L4g0/MiDispositivoMIDI_A3C/04_img/bot.png

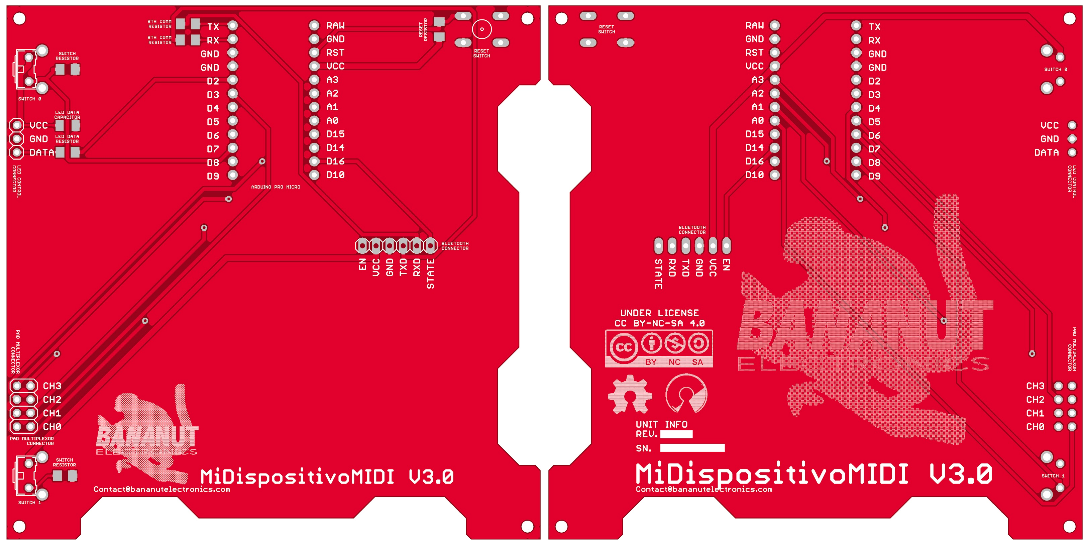
04_img/bot.png
