L4g0/MiDispositivoMIDI_A3C/04_img/front.jpg

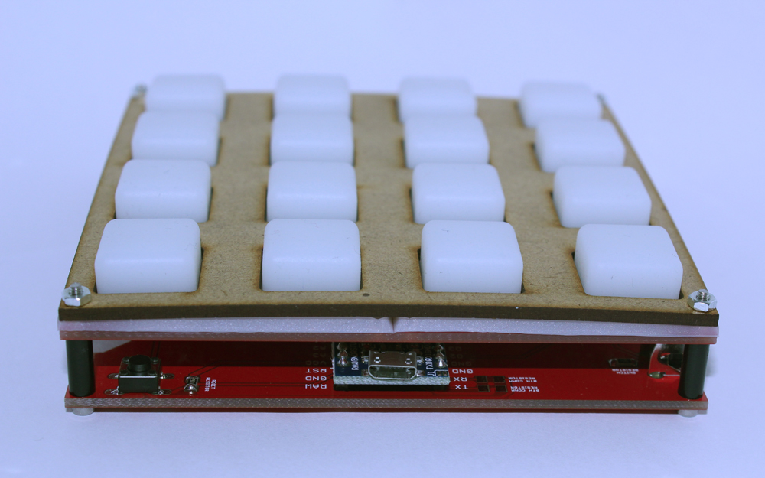
04_img/front.jpg
