L4g0/MiDispositivoMIDI_A3C/04_img/green.jpg

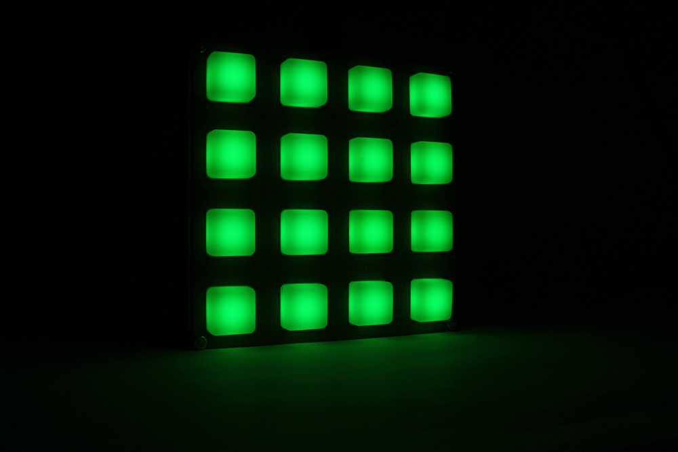
04_img/green.jpg
