L4g0/MiDispositivoMIDI_A3C/04_img/MDM_V3_HW_Render.PNG

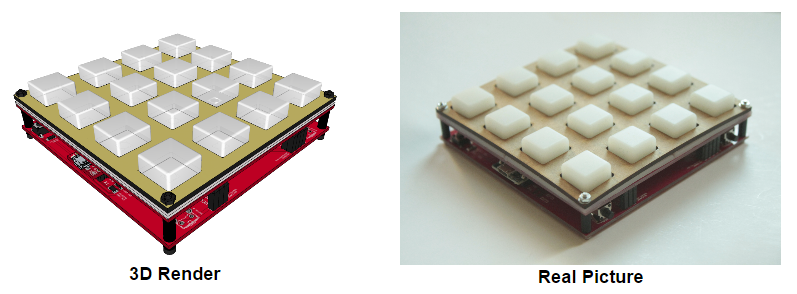
04_img/MDM_V3_HW_Render.PNG
