L4g0/MiDispositivoMIDI_A3C/04_img/MDM_V3_INTRO_Workshop_0.png

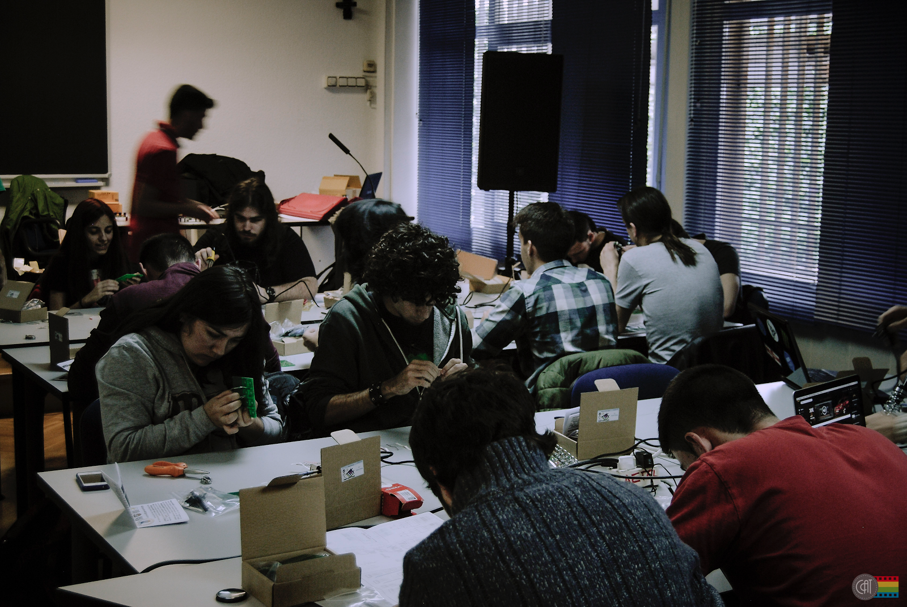
04_img/MDM_V3_INTRO_Workshop_0.png
