L4g0/MiDispositivoMIDI_A3C/04_img/MDM_V3_INTROWorkshop_1.png

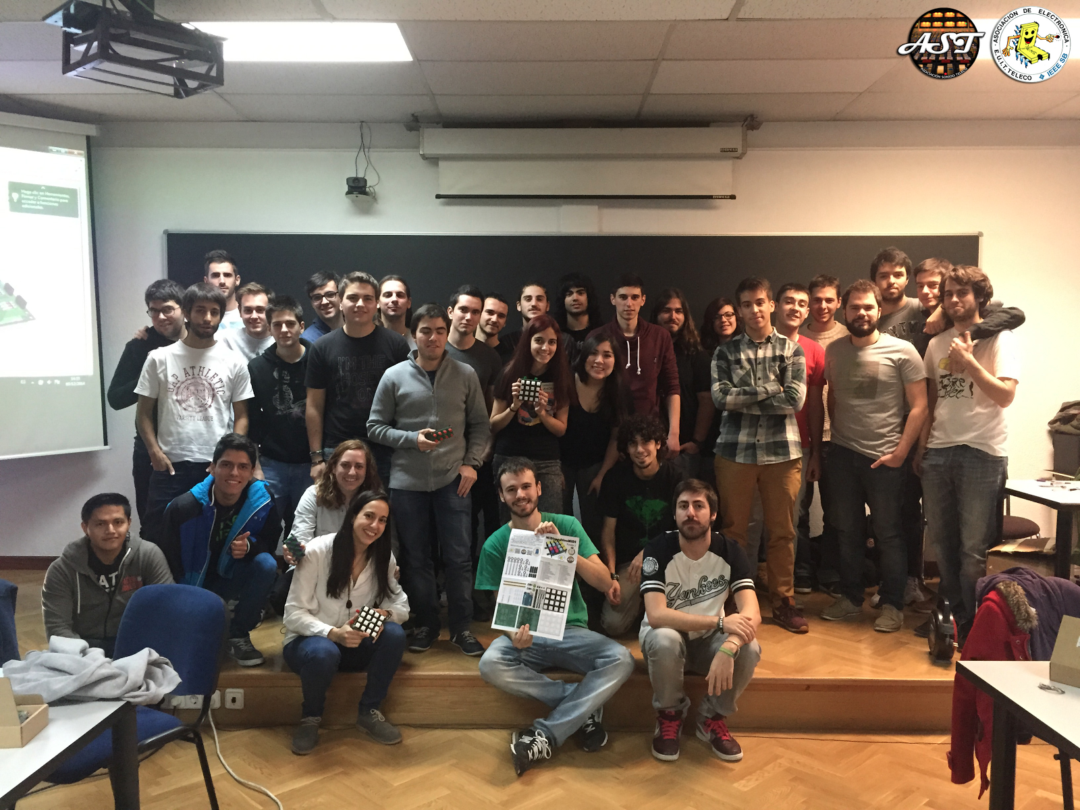
04_img/MDM_V3_INTROWorkshop_1.png
