L4g0/MiDispositivoMIDI_A3C/04_img/touchpads.JPG

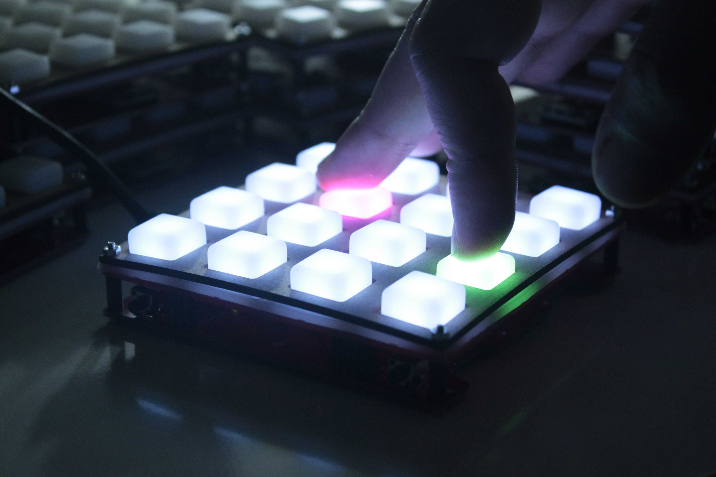
04_img/touchpads.JPG
