L4g0/MiDispositivoMIDI_A3C/04_img/yellow.jpg

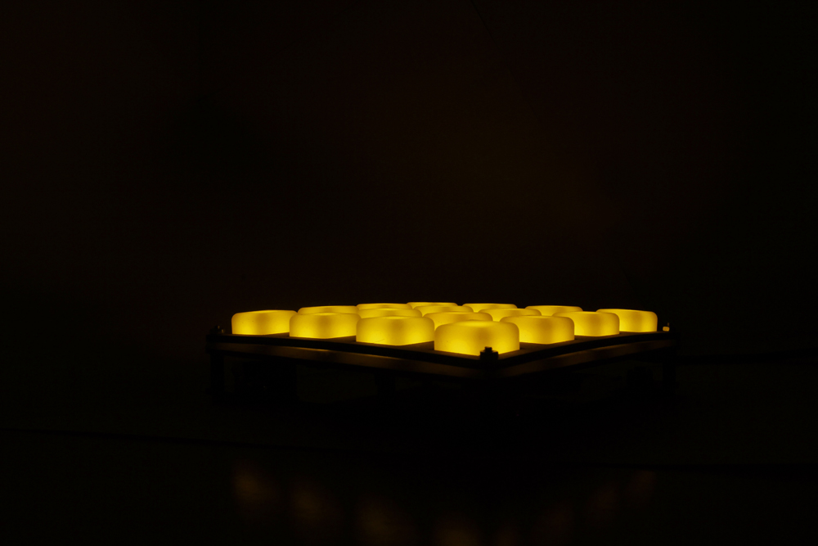
04_img/yellow.jpg
