L4g0/MiDispositivoMIDI_A3C/04_img/components.png

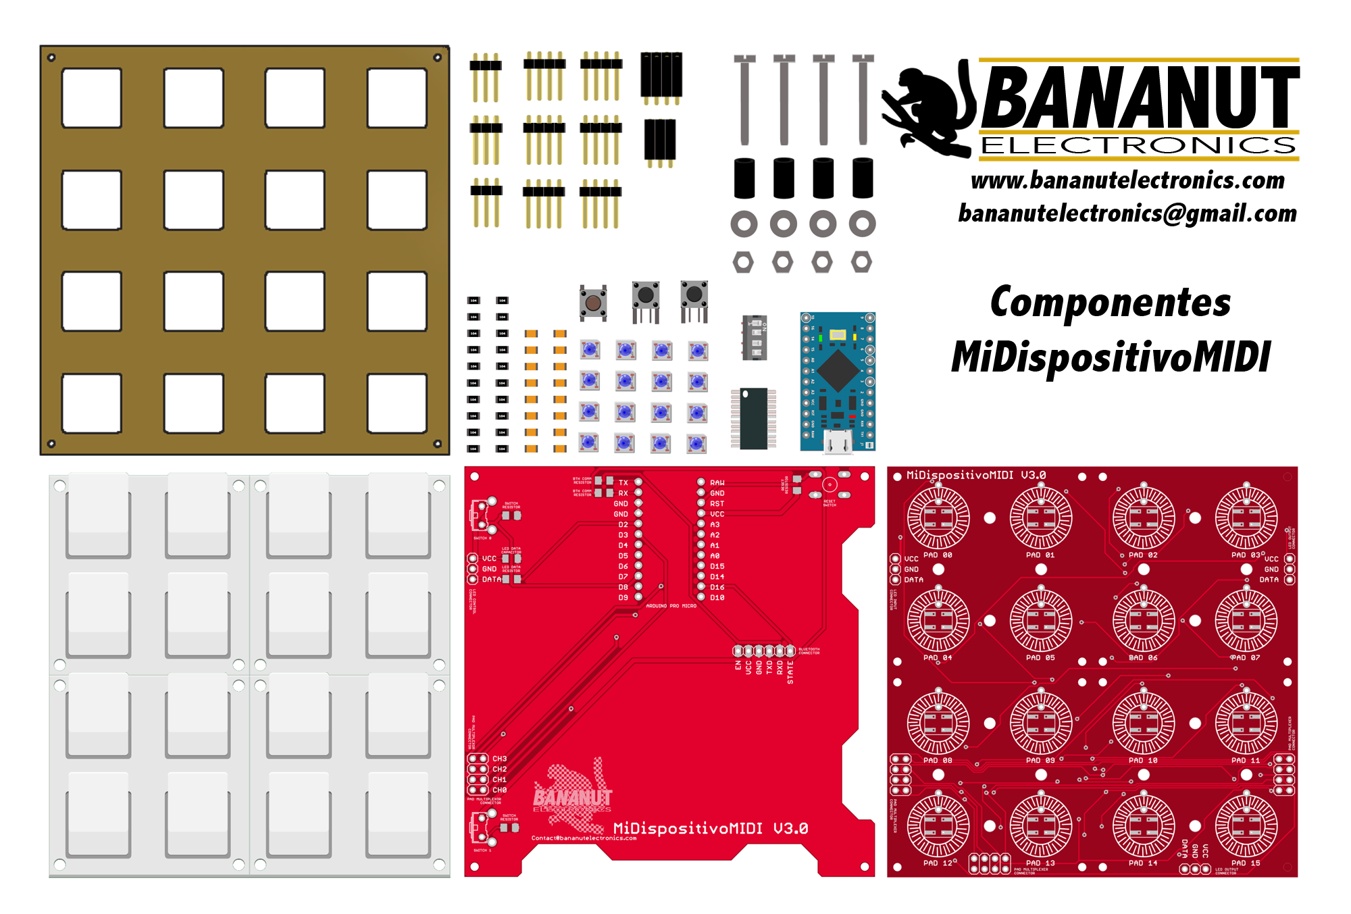
04_img/components.png
