L4g0/MiDispositivoMIDI_A3C/02_hw/01_MDM_V3_LEDPad/tags/A_MDM_V3_LEDPad/MDM_V3_LEDPad_A.sch

## EAGLE design 02_hw/01_MDM_V3_LEDPad/tags/A_MDM_V3_LEDPad/MDM_V3_LEDPad_A.sch (2017-02-17)

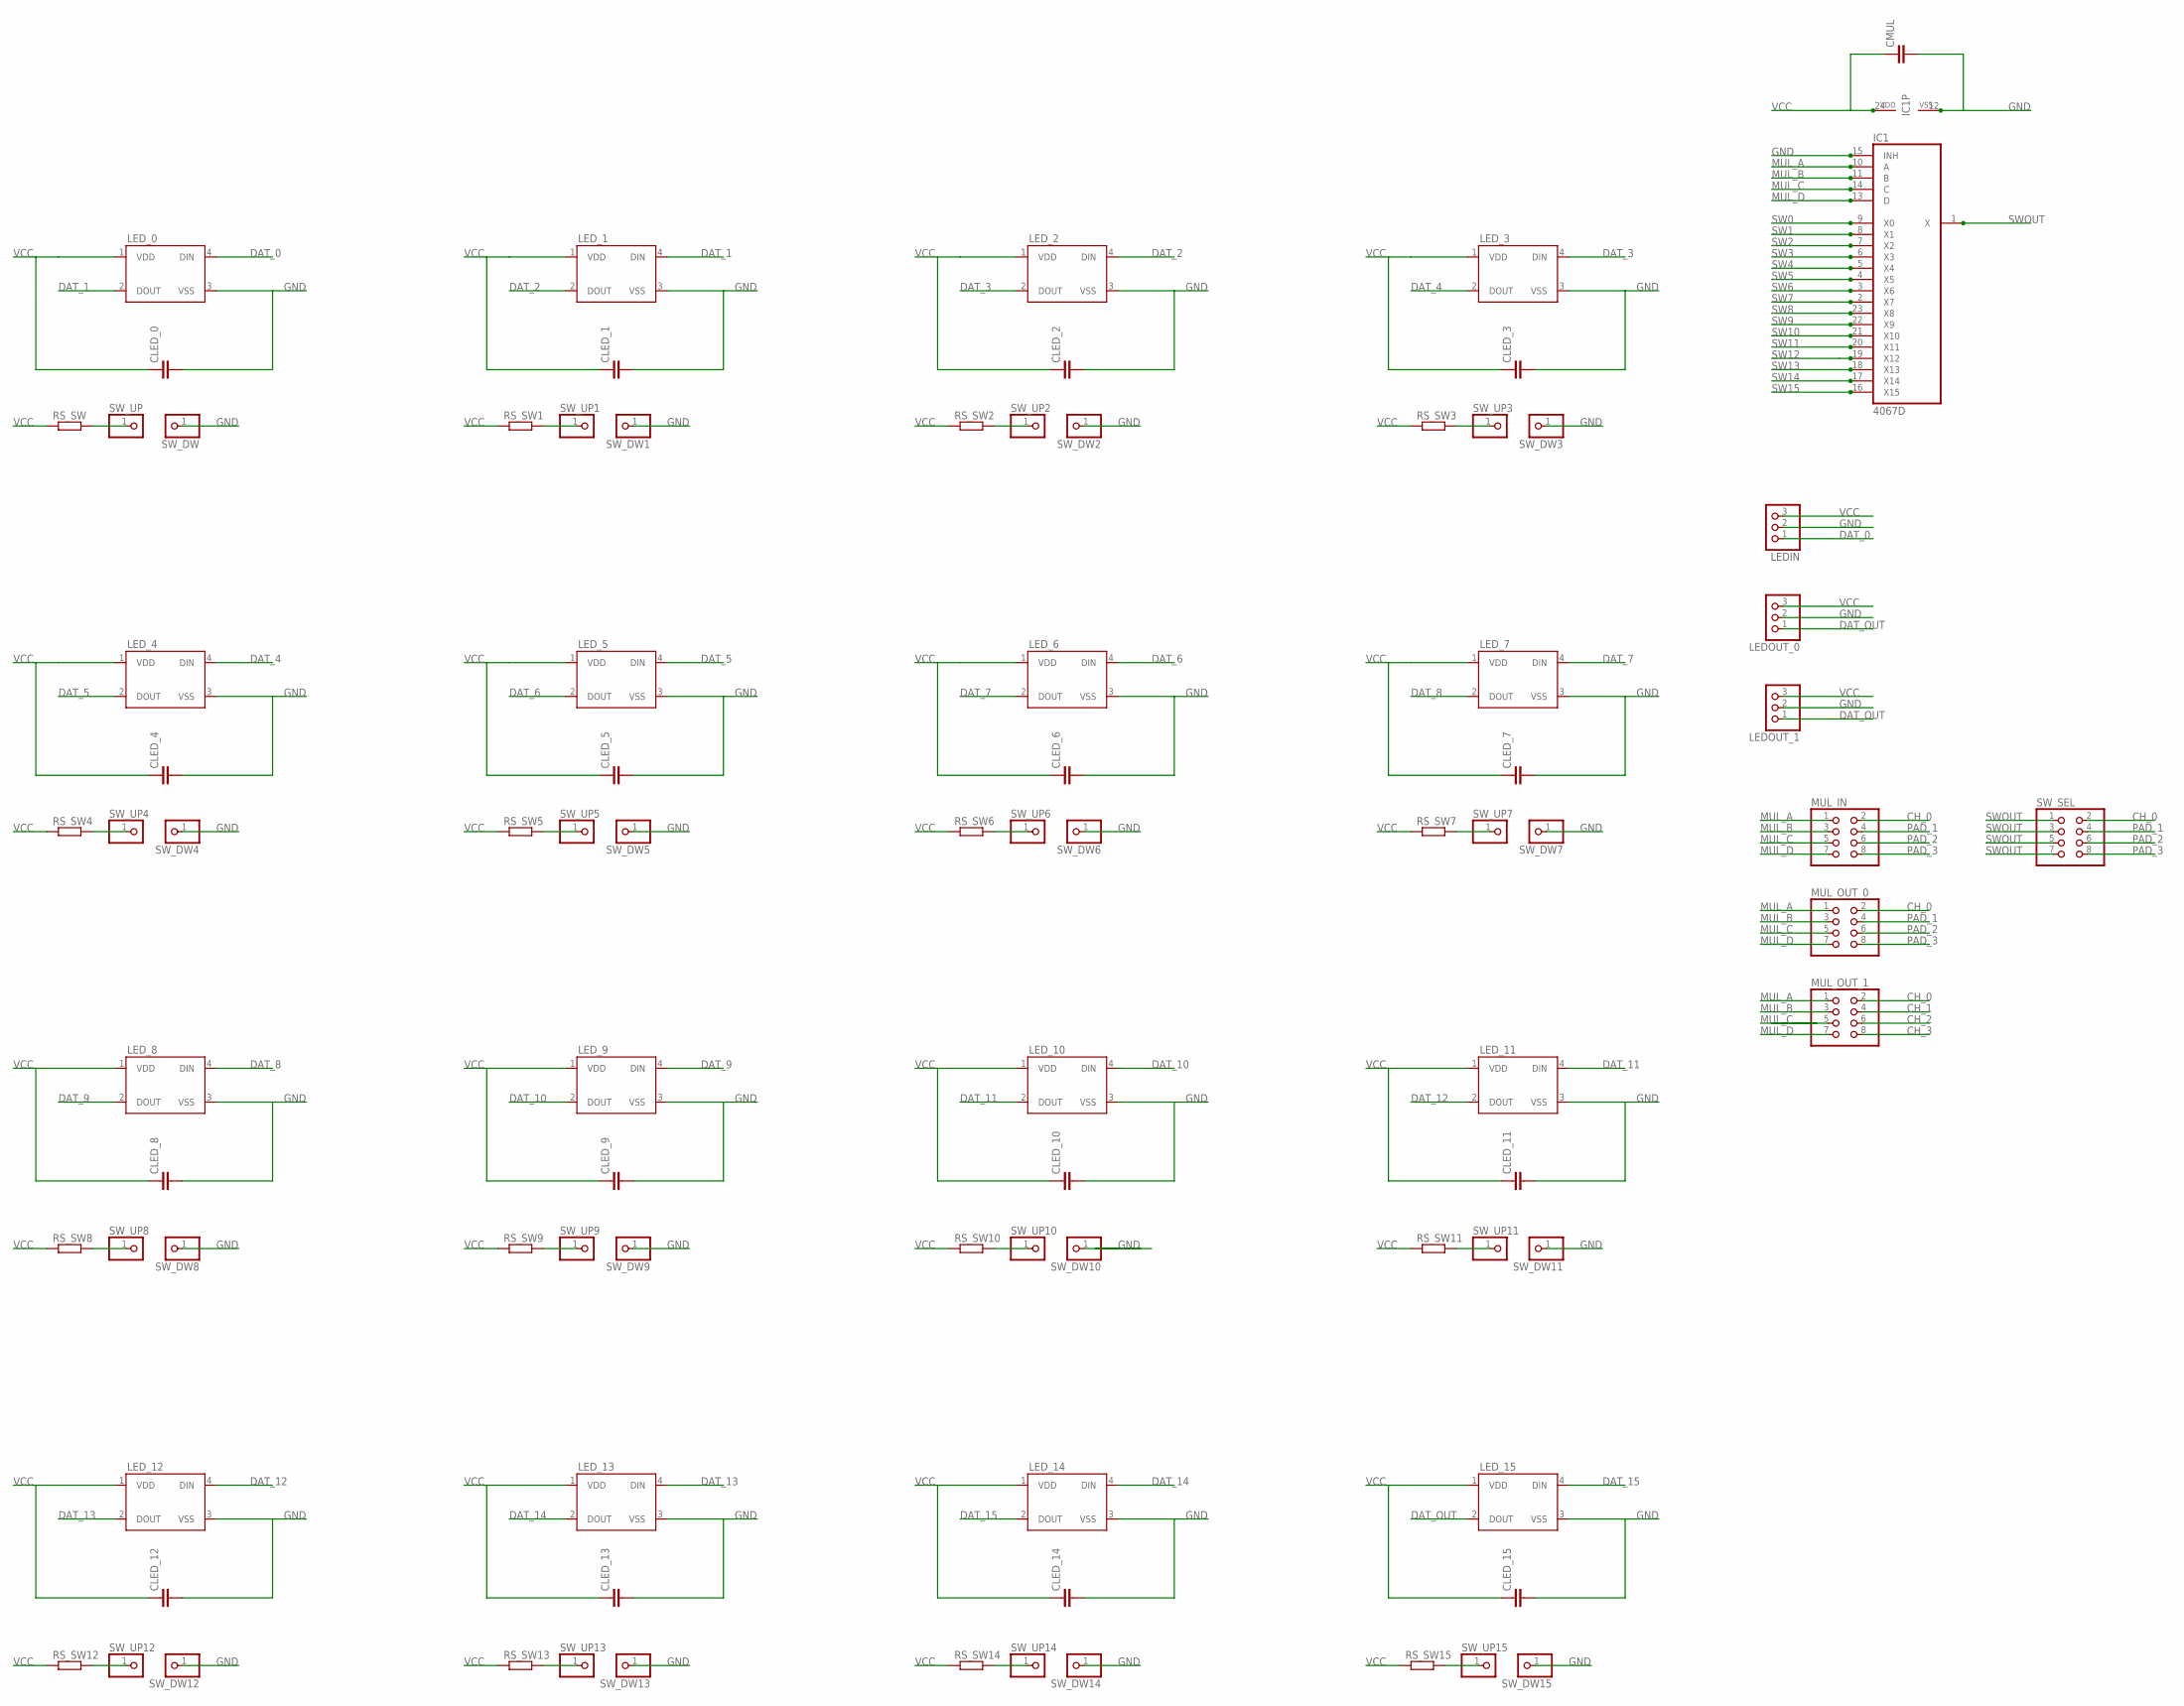
[picture p59: schematic MDM_V3_LEDPad_A.sch]

Parts:
CLED_0, CLED_1, CLED_2, CLED_3, CLED_4, CLED_5, CLED_6, CLED_7, CLED_8, CLED_9, CLED_10, CLED_11, CLED_12, CLED_13, CLED_14, CLED_15: C-EUC1206K; C1206K
CMUL: C-EUC1206K; C1206K
IC1: 4067D; SO24W
LEDIN: PINHD-1X3; 1X03
LEDOUT_0, LEDOUT_1: PINHD-1X3; 1X03
LED_0, LED_1, LED_2, LED_3, LED_4, LED_5, LED_6, LED_7, LED_8, LED_9, LED_10, LED_11, LED_12, LED_13, LED_14, LED_15: WS2812B
MUL_IN: PINHD-2X4; 2X04
MUL_OUT_0, MUL_OUT_1: PINHD-2X4; 2X04
RS_SW, RS_SW1, RS_SW2, RS_SW3, RS_SW4, RS_SW5, RS_SW6, RS_SW7, RS_SW8, RS_SW9, RS_SW10, RS_SW11, RS_SW12, RS_SW13, RS_SW14, RS_SW15: R-EU_R1206; R1206
SW_DW, SW_DW1, SW_DW2, SW_DW3, SW_DW4, SW_DW5, SW_DW6, SW_DW7, SW_DW8, SW_DW9, SW_DW10, SW_DW11, SW_DW12, SW_DW13, SW_DW14, SW_DW15: PINHD-1X1CB; 1X01-CLEANBIG
SW_SEL: PINHD-2X4; 2X04
SW_UP, SW_UP1, SW_UP2, SW_UP3, SW_UP4, SW_UP5, SW_UP6, SW_UP7, SW_UP8, SW_UP9, SW_UP10, SW_UP11, SW_UP12, SW_UP13, SW_UP14, SW_UP15: PINHD-1X1CB; 1X01-CLEANBIG

Connections:
CH_0: MUL_IN.2, MUL_OUT_0.2, MUL_OUT_1.2, SW_SEL.2
CH_1: MUL_OUT_1.4
CH_2: MUL_OUT_1.6
CH_3: MUL_OUT_1.8
DAT_0: LEDIN.1, LED_0.4 (DIN)
DAT_1: LED_0.2 (DOUT), LED_1.4 (DIN)
DAT_2: LED_1.2 (DOUT), LED_2.4 (DIN)
DAT_3: LED_2.2 (DOUT), LED_3.4 (DIN)
DAT_4: LED_3.2 (DOUT), LED_4.4 (DIN)
DAT_5: LED_4.2 (DOUT), LED_5.4 (DIN)
DAT_6: LED_5.2 (DOUT), LED_6.4 (DIN)
DAT_7: LED_6.2 (DOUT), LED_7.4 (DIN)
DAT_8: LED_7.2 (DOUT), LED_8.4 (DIN)
DAT_9: LED_8.2 (DOUT), LED_9.4 (DIN)
DAT_10: LED_9.2 (DOUT), LED_10.4 (DIN)
DAT_11: LED_10.2 (DOUT), LED_11.4 (DIN)
DAT_12: LED_11.2 (DOUT), LED_12.4 (DIN)
DAT_13: LED_12.2 (DOUT), LED_13.4 (DIN)
DAT_14: LED_13.2 (DOUT), LED_14.4 (DIN)
DAT_15: LED_14.2 (DOUT), LED_15.4 (DIN)
DAT_OUT: LEDOUT_0.1, LEDOUT_1.1, LED_15.2 (DOUT)
GND: CLED_0.2, CLED_1.2, CLED_2.2, CLED_3.2, CLED_4.2, CLED_5.2, CLED_6.2, CLED_7.2, CLED_8.2, CLED_9.2, CLED_10.2, CLED_11.2, CLED_12.2, CLED_13.2, CLED_14.2, CLED_15.2, CMUL.2, IC1.12 (VSS), IC1.15 (INH), LEDIN.2, LEDOUT_0.2, LEDOUT_1.2, LED_0.3 (VSS), LED_1.3 (VSS), LED_2.3 (VSS), LED_3.3 (VSS), LED_4.3 (VSS), LED_5.3 (VSS), LED_6.3 (VSS), LED_7.3 (VSS), LED_8.3 (VSS), LED_9.3 (VSS), LED_10.3 (VSS), LED_11.3 (VSS), LED_12.3 (VSS), LED_13.3 (VSS), LED_14.3 (VSS), LED_15.3 (VSS), SW_DW.1, SW_DW1.1, SW_DW2.1, SW_DW3.1, SW_DW4.1, SW_DW5.1, SW_DW6.1, SW_DW7.1, SW_DW8.1, SW_DW9.1, SW_DW10.1, SW_DW11.1, SW_DW12.1, SW_DW13.1, SW_DW14.1, SW_DW15.1
MUL_A: IC1.10 (A), MUL_IN.1, MUL_OUT_0.1, MUL_OUT_1.1
MUL_B: IC1.11 (B), MUL_IN.3, MUL_OUT_0.3, MUL_OUT_1.3
MUL_C: IC1.14 (C), MUL_IN.5, MUL_OUT_0.5, MUL_OUT_1.5
MUL_D: IC1.13 (D), MUL_IN.7, MUL_OUT_0.7, MUL_OUT_1.7
PAD_1: MUL_IN.4, MUL_OUT_0.4, SW_SEL.4
PAD_2: MUL_IN.6, MUL_OUT_0.6, SW_SEL.6
PAD_3: MUL_IN.8, MUL_OUT_0.8, SW_SEL.8
SW: RS_SW.2, SW_UP.1
SW0: IC1.9 (X0)
SW1: IC1.8 (X1), RS_SW1.2, SW_UP1.1
SW2: IC1.7 (X2), RS_SW2.2, SW_UP2.1
SW3: IC1.6 (X3), RS_SW3.2, SW_UP3.1
SW4: IC1.5 (X4), RS_SW4.2, SW_UP4.1
SW5: IC1.4 (X5), RS_SW5.2, SW_UP5.1
SW6: IC1.3 (X6), RS_SW6.2, SW_UP6.1
SW7: IC1.2 (X7), RS_SW7.2, SW_UP7.1
SW8: IC1.23 (X8), RS_SW8.2, SW_UP8.1
SW9: IC1.22 (X9), RS_SW9.2, SW_UP9.1
SW10: IC1.21 (X10), RS_SW10.2, SW_UP10.1
SW11: IC1.20 (X11), RS_SW11.2, SW_UP11.1
SW12: IC1.19 (X12), RS_SW12.2, SW_UP12.1
SW13: IC1.18 (X13), RS_SW13.2, SW_UP13.1
SW14: IC1.17 (X14), RS_SW14.2, SW_UP14.1
SW15: IC1.16 (X15), RS_SW15.2, SW_UP15.1
SWOUT: IC1.1 (X), SW_SEL.1, SW_SEL.3, SW_SEL.5, SW_SEL.7
VCC: CLED_0.1, CLED_1.1, CLED_2.1, CLED_3.1, CLED_4.1, CLED_5.1, CLED_6.1, CLED_7.1, CLED_8.1, CLED_9.1, CLED_10.1, CLED_11.1, CLED_12.1, CLED_13.1, CLED_14.1, CLED_15.1, CMUL.1, IC1.24 (VDD), LEDIN.3, LEDOUT_0.3, LEDOUT_1.3, LED_0.1 (VDD), LED_1.1 (VDD), LED_2.1 (VDD), LED_3.1 (VDD), LED_4.1 (VDD), LED_5.1 (VDD), LED_6.1 (VDD), LED_7.1 (VDD), LED_8.1 (VDD), LED_9.1 (VDD), LED_10.1 (VDD), LED_11.1 (VDD), LED_12.1 (VDD), LED_13.1 (VDD), LED_14.1 (VDD), LED_15.1 (VDD), RS_SW.1, RS_SW1.1, RS_SW2.1, RS_SW3.1, RS_SW4.1, RS_SW5.1, RS_SW6.1, RS_SW7.1, RS_SW8.1, RS_SW9.1, RS_SW10.1, RS_SW11.1, RS_SW12.1, RS_SW13.1, RS_SW14.1, RS_SW15.1
